SolidEva/noisedeck/cad/stls/case_assembly-topcase_lower_btrfld_support_outer.stl

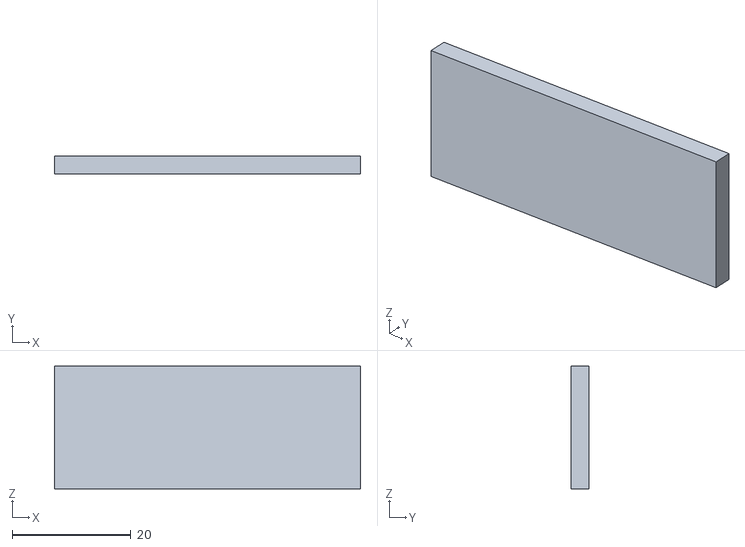
[picture p22: CAD file, 2026-04-02]
cad/stls/case_assembly-topcase_lower_btrfld_support_outer.stl
51.5 x 3.00 x 20.7
