SolidEva/noisedeck/cad/noisedeck.FCStd

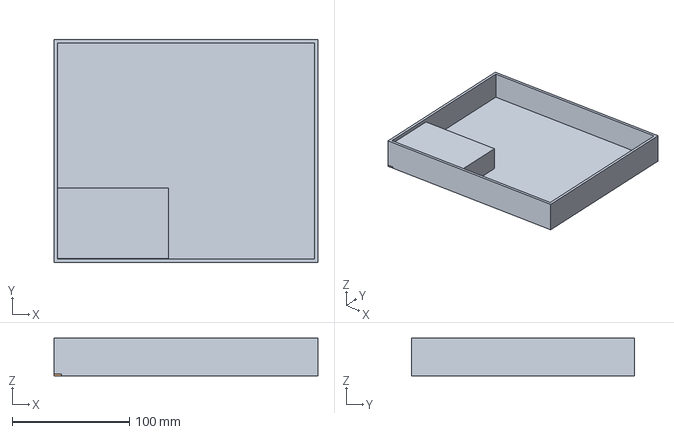
[picture p23: CAD file, 2026-04-30]
cad/noisedeck.FCStd
225.0 x 190.0 x 32.0 mm
general_layout
hinge_half
