SolidEva/noisedeck/cad/btrfld.FCStd

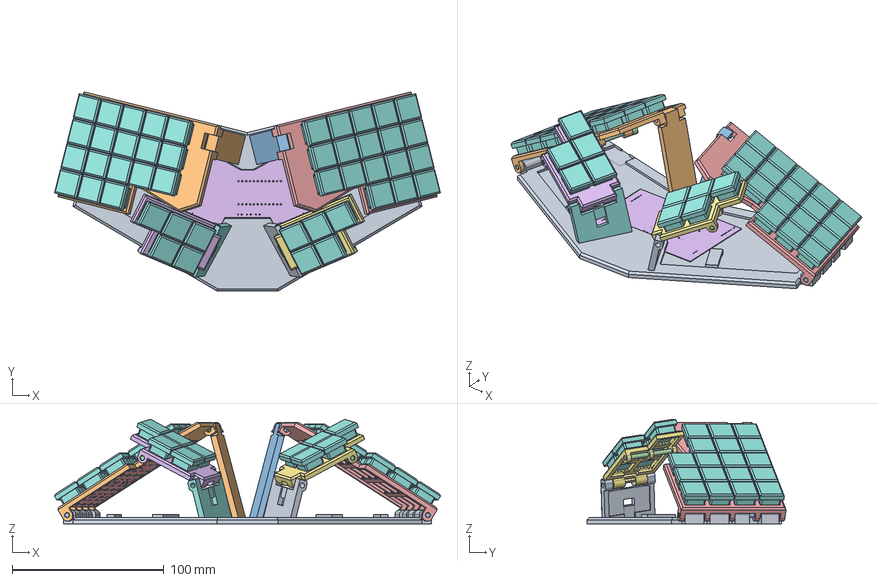
[picture p24: CAD file, 2026-04-18]
cad/btrfld.FCStd
254.2 x 131.3 x 68.8 mm
Baseplate
BaseplateBodyRod x 2
BodyThumbRod001 x 2
Body_mirrored
ThumbLeft
ThumbLeft_mirrored002
ThumbExtensionLeft
ThumbExtensionLeft_mirrored
BodyBaseplateSupportLeft
BodyBaseplateSupportLeft_mirrored
BodyThumRodCap x 2
Pcb_205d
Pcb_ce66
Pcb_fe2c
choc_key_and_cap x 46
